jonbro/Audcalc/Firmware/Instrument.cc

#include "Instrument.h"
#include "AudioSampleSecondbloop.h"
#include "GlobalDefines.h"
#include "GrooveBox.h"
#include "audio/random.h"

static const uint16_t kPitchTableStart = 128 * 128;
static const uint16_t kOctave = 12 * 128;

void Instrument::Init(Midi *_midi, int16_t *temp_buffer)
{
    osc.Init(temp_buffer);
    currentSegment = ENV_SEGMENT_COMPLETE;
    osc.set_pitch(60<<7);
    osc.set_shape(MACRO_OSC_SHAPE_WAVE_MAP);
    osc.set_parameters(0,0);
    envPhase = 0;
    svf.Init();
    // svf.set_mode(SVF_MODE_HP);
    // svf.set_punch(0);
    midi = _midi;
    phase_ = 0;    
    sampleOffset = 0;
    env.Init();
    env.Trigger(ADSR_ENV_SEGMENT_DEAD);
    env2.Init();
    env2.Trigger(ADSR_ENV_SEGMENT_DEAD);
    portamentoEnv.Init();
    portamentoEnv.Trigger(ADSR_ENV_SEGMENT_DEAD);
}

const char *macroparams[16] = { 
    "Timb", "Filt", "VlPn", "Ptch",
    "Env", "EnvF", "EnvP", "EnvT",
    "?", "?", "?", "?",
    "?", "?", "FLTO", "TYPE"
};

const char *sampleparams[16] = { 
    "I/O", "FILT", "VlPn", "Ptch",
    "Env", "EnvF", "EnvP", "EnvT",
    "lop", "?", "?", "?",
    "?", "?", "FLTO", "TYPE"
};

// Values are defined in number of samples
void Instrument::SetAHD(uint32_t attackTime, uint32_t holdTime, uint32_t decayTime)
{
    this->attackTime = attackTime;
    this->holdTime = holdTime;
    this->decayTime = decayTime;
    env.Update(0x2b, 0x7f);
}

uint32_t Instrument::ComputePhaseIncrement(int16_t midi_pitch) {
  if (midi_pitch >= kPitchTableStart) {
    midi_pitch = kPitchTableStart - 1;
  }
  
  int32_t ref_pitch = midi_pitch;
  ref_pitch -= kPitchTableStart;
  
  size_t num_shifts = 0;
  while (ref_pitch < 0) {
    ref_pitch += kOctave;
    ++num_shifts;
  }
  
  uint32_t a = lut_sample_increments[ref_pitch >> 4];
  uint32_t b = lut_sample_increments[(ref_pitch >> 4) + 1];
  uint32_t phase_increment = a + \
      (static_cast<int32_t>(b - a) * (ref_pitch & 0xf) >> 4);
  phase_increment >>= num_shifts;
  return phase_increment;
}
q15_t Instrument::GetRawLfoValue()
{
    switch(lfo_shape)
    {
        case Lfo_Shape_RampUp:
            return (int16_t)(lfo_phase >> 16);
        case Lfo_Shape_RampDown:
            return -(int16_t)(lfo_phase >> 16);
        case Lfo_Shape_Triangle:
        {
            uint32_t p = lfo_phase;
            if (p >= 0x80000000u) p = 0xFFFFFFFFu - p;
            return (int16_t)((p >> 15) - 32767);
        }
        case Lfo_Shape_Square:
            return lfo_phase >= 0x80000000u ? (int16_t)0x7fff : (int16_t)-0x7fff;
        case Lfo_Shape_Random:
            return lfo_random_value;
        case Lfo_Shape_SampleGlide:
        {
            int32_t t = lfo_phase >> 16;
            return (int16_t)(((int32_t)lfo_random_prev * (65535 - t) + (int32_t)lfo_random_value * t) >> 16);
        }
        default: // Lfo_Shape_Sine
            return Interpolate824(wav_sine, lfo_phase);
    }
}
q15_t Instrument::GetLfoState()
{
    return mult_q15(GetRawLfoValue(), lfo_depth);
}
void __not_in_flash_func(Instrument::Render)(const uint8_t* sync, int16_t* buffer, size_t size)
{    
    q15_t param1_withMods = param1Base;
    q15_t param2_withMods = param2Base;
    q15_t cutoffWithMods = mainCutoff;
    q15_t pitchWithMods = pitch = Mix(pitchStart, pitchTarget, 65535-portamentoAmt);
    panWithMods = panning;
    volumeWithMods = volume;
    q15_t lfo = GetLfoState();
    switch(lfo1Target)
    {
        case Lfo_Target_Volume:
        {
            // lfo_depth maxes at ~0x3fff, so <<1 gives full q15 range.
            q15_t raw = GetRawLfoValue();
            q15_t norm = (raw >> 1) + 0x4000;  // [-1,1] -> [0,1] in q15
            q15_t D = lfo_depth << 1;           // full-range depth
            // scale: 1.0 at peak, (1-D) at trough
            q15_t scale = (0x7fff - D) + mult_q15(D, norm);
            volumeWithMods = mult_q15(volume, scale);
            break;
        }
        case Lfo_Target_Timbre:
            param1_withMods = add_q15(param1_withMods, lfo);
            break;
        case Lfo_Target_Color:
            param2_withMods = add_q15(param2_withMods, lfo);
            break;
        case Lfo_Target_Cutoff:
            cutoffWithMods = add_q15(cutoffWithMods, lfo);
            break;
        case Lfo_Target_Pitch:
            pitchWithMods = pitchWithMods+(lfo>>4);
            break;
        case Lfo_Target_Pan:
            panWithMods = add_q15(panWithMods, lfo);
            break;
        default:
            break;
    }

    // could alternately use tick rate stuff. might be way better
    // fast 4bf0000
    // slow fffff
    // holy hell what the fuck is this code, seriously :0
    // should like, maybe, move this into some class or something :P 
    uint32_t lfoPhaseIncrement = lut_tempo_phase_increment[songData->GetBpm()];
    // 24ppq
    lfoPhaseIncrement = lfoPhaseIncrement + (lfoPhaseIncrement>>1);
    lfoPhaseIncrement = lfoPhaseIncrement/((lfo_rate>>4)+2);
    //int32_t phaseOff = ((uint32_t)(0xffff-Interpolate824(lut_env_expo, (0x7fff-lfo_rate)<<16))<<13)-0x7fffff; 
    uint32_t old_phase = lfo_phase;
    lfo_phase += lfoPhaseIncrement;
    if (lfo_phase < old_phase) {  // wrapped — update S&H/SampleGlide random values
        lfo_random_prev = lfo_random_value;
        lfo_random_value = stmlib::Random::GetSample();
    }

    for (size_t i = 0; i < 2; i++)
    {
        EnvTargets t = i==0?env1Target:env2Target;
        int16_t depth = i==0?env1Depth:env2Depth;
        depth = (depth-0x4000)*2; // center at zero
        ADSREnvelope* e = i==0?&env:&env2;
        switch (t)
        {
            case Target_Volume:
                break;
            case Target_Timbre:
                param1_withMods = add_q15(param1_withMods, mult_q15(depth, e->valueLin()>>1));
                break;
            case Target_Color:
                param2_withMods = add_q15(param2_withMods, mult_q15(depth, e->valueLin()>>1));
                break;
            case Target_Cutoff:
                cutoffWithMods = add_q15(cutoffWithMods, mult_q15(depth, e->valueLin()>>1));
                break;
            case Target_Pitch:
                pitchWithMods = pitchWithMods+(mult_q15(depth, e->value()>>1)>>4);
                break;
            case Target_Pan:
                panWithMods = add_q15(panWithMods, mult_q15(depth, e->valueLin()>>1));
                break;
            default:
                break;
        }
    }
    
    if(param1_withMods < 0)
    {
        param1_withMods = 0;
    }
    if(param2_withMods < 0)
    {
        param2_withMods = 0;
    }
    if(cutoffWithMods < 0)
    {
        cutoffWithMods = 0;
    }
    pWithMods = cutoffWithMods; 
    svf.set_frequency(cutoffWithMods);

    if(instrumentType == INSTRUMENT_SAMPLE)
    {
        uint32_t filesize = ffs_file_size(GetFilesystem(), file);
        if(!file || filesize == 0 || sampleSegment == SMP_COMPLETE)
        {
            memset(buffer, 0, SAMPLES_PER_BLOCK*2);
            return;
        }
        // double check the file length
        if(!file->initialized || sampleOffset*2 > file->filesize)
            sampleSegment = SMP_COMPLETE;
        if(sampleSegment == SMP_COMPLETE)
        {
            for(int i=0;i<SAMPLES_PER_BLOCK;i++)
            {
                buffer[i] = 0;
            }
            return;
        }

        // this is too slow to do in the loop - which unfortunately makes
        // handling higher octaves quite difficult
        // one thing I could do is add a special read mode to change the stepping in the ffs_read to match the phase increment - i.e. read 1, skip 1 or something like this?
        // int16_t wave[128*5] = {0}; // lets just get 5 octaves worth? thats only 2k, we should be able to spare it, lol
        // ffs_seek(GetFilesystem(), file, sampleOffset*2);
        // // clamp the read amount to the maximum filesize
        // // todo: add a ffs_read that takes a per read stride, so I can fill this more easily, and don't need to load more than necessary
        // uint16_t readAmount = (sampleOffset*2+2*128*5)>filesize?filesize-sampleOffset*2:2*128*5;
        // ffs_read(GetFilesystem(), file, wave, readAmount);
        uint32_t startingSampleOffset = sampleOffset;
        for(int i=0;i<SAMPLES_PER_BLOCK;i++)
        {
            if(sampleOffset > sampleEnd - 1)
            {
                if(loopMode == INSTRUMENT_LOOPMODE_NONE)
                {
                    sampleSegment = SMP_COMPLETE;
                    buffer[i] = 0;
                    continue;
                }
                else
                {
                    while(sampleOffset*2 > filesize - 1)
                    {
                        sampleOffset -= filesize/2;
                    }
                }
            }
            int16_t wave;
            ffs_seek(GetFilesystem(), file, sampleOffset*2);
            ffs_read(GetFilesystem(), file, &wave, 2);

            phase_ += phase_increment;
            sampleOffset+=(phase_>>25);
            phase_-=(phase_&(0xfe<<24));

            buffer[i] = wave;//[sampleOffset-startingSampleOffset];
            
            if(microFade < 0xfa)
            {
                buffer[i] = (((int32_t)buffer[i]*microFade)>>8);
                microFade += 0xa;
            }
            // else
            // {
            //     lastSample = buffer[i];
            // }
        }
    }
    else if(instrumentType == INSTRUMENT_MACRO)
    {
        osc.set_pitch(pitchWithMods);
        osc.set_parameter_1(param1_withMods);
        osc.set_parameter_2(param2_withMods);
        osc.Render(sync, buffer, SAMPLES_PER_BLOCK);
    }
    RenderGlobal(sync, buffer, size);
}
void Instrument::RenderGlobal(const uint8_t* sync, int16_t* buffer, size_t size)
{
    int32_t volDelta = (int32_t)volumeWithMods - (int32_t)prevVolumeWithMods;
    for(int i=0;i<SAMPLES_PER_BLOCK;i++)
    {
        lastenv2val = env2.Render();
        lastenvval = env.Render();
        portamentoAmt = portamentoEnv.Render();
        q15_t envval = lastenvval >> 1;
        if(enable_env)
        {
            buffer[i] = mult_q15(buffer[i], envval);
        }
        // buffer[i] = Interpolate88(ws_violent_overdrive, buffer[i] + 32768);

        buffer[i] = svf.Process(buffer[i]);
        
        // not sure why distortion isn't working, revisit at some point
        // int32_t shiftedSample = mult_q15(buffer[i], f32_to_q15(0.5));// + distortionAmount; // I think this is the overdrive amount? 
        // buffer[i] = Interpolate88(ws_moderate_overdrive, shiftedSample);
        // buffer[i] = mult_q15(buffer[i], f32_to_q15(1));
        buffer[i] = mult_q15(buffer[i], retriggerVolume);
        q15_t vol_i = prevVolumeWithMods + volDelta * i / SAMPLES_PER_BLOCK;
        buffer[i] = mult_q15(buffer[i], vol_i);
    }
    prevVolumeWithMods = volumeWithMods;
}
bool Instrument::IsPlaying()
{
    if(env.segment() == ADSR_ENV_SEGMENT_DEAD)
        return false;
    if(instrumentType == INSTRUMENT_SAMPLE && sampleSegment == SMP_COMPLETE)
        return false;
    return true;
}

void Instrument::SetOscillator(uint8_t oscillator)
{
    osc.set_shape((MacroOscillatorShape)oscillator);
}

void Instrument::UpdateVoiceData(VoiceData &voiceData)
{
    uint8_t pv[VoiceData::PARAM_CACHE_SIZE];
    voiceData.FillResolvedParamCache(playingStep, playingPattern, lastPressedKey, pv, !liveTriggered);

    lfo1Target = (LfoTargets)(((uint16_t)pv[Lfo1Target] * Lfo_Target_Count) >> 8);

    delaySend = pv[DelaySend];
    reverbSend = pv[ReverbSend];
    volume = ((q15_t)pv[Volume]) << 7;
    panning = ((q15_t)pv[Pan]) << 7;
    portamentoParamAmt = pv[Portamento];
    fineTuneParamAmt = pv[FineTune];
    q15_t env1A = (q15_t)pv[AttackTime] << 7;
    q15_t env1D = (q15_t)pv[DecayTime] << 7;
    q15_t env2A = (q15_t)pv[AttackTime2] << 7;
    q15_t env2D = (q15_t)pv[DecayTime2] << 7;
    q15_t lfoState = GetLfoState();
    switch(lfo1Target)
    {
        case Lfo_Target_Env1Attack:
            env1A = add_q15(env1A, lfoState);
            break;
        case Lfo_Target_Env2Attack:
            env2A = add_q15(env2A, lfoState);
            break;
        case Lfo_Target_Env1Decay:
            env1D = add_q15(env1D, lfoState);
            break;
        case Lfo_Target_Env2Decay:
            env2D = add_q15(env1A, lfoState);
            break;
        case Lfo_Target_Env12Attack:
            env1A = add_q15(env1A, lfoState);
            env2A = add_q15(env2A, lfoState);
            break;
        case Lfo_Target_Env12Decay:
            env1D = add_q15(env1D, lfoState);
            env2D = add_q15(env1D, lfoState);
            break;
        default:
            break;
    }
    if(env1D < 0) env1D = 0;
    if(env1A < 0) env1A = 0;
    if(env2D < 0) env2D = 0;
    if(env2A < 0) env2A = 0;
    if(instrumentType == INSTRUMENT_SAMPLE || instrumentType == INSTRUMENT_MACRO)
    {
        env.Update(env1A>>8, env1D>>8);
        env2.Update(env2A>>8, env2D>>8);
        lfo_depth = (pv[LFODepth] >> 1) << 7;
        lfo_rate = (pv[LFORate] >> 1) << 7;
        lfo_shape = (pv[Lfo1Shape] * Lfo_Shape_Count) >> 8;
        mainCutoff = (pv[Cutoff] >> 1) << 7;
        svf.set_frequency(add_q15(mainCutoff, lastenv2val>>1));
        svf.set_resonance((pv[Resonance] >> 1) << 7);
        env1Target = (EnvTargets)(((uint16_t)pv[Env1Target] * Target_Count) >> 8);
        env1Depth = (q15_t)pv[Env1Depth] << 7;
        env2Target = (EnvTargets)(((uint16_t)pv[Env2Target] * Target_Count) >> 8);
        env2Depth = (q15_t)pv[Env2Depth] << 7;
        distortionAmount = (q15_t)pv[DelaySend] << 7;
    }
    if(voiceData.GetInstrumentType() == INSTRUMENT_MACRO)
    {
        param1Base = (q15_t)pv[Timbre] << 7;
        param2Base = (q15_t)pv[Color] << 7;
    }
}

void __not_in_flash_func(Instrument::TempoPulse)()
{
    if(TickRetriggers())
        Retrigger();
}
void Instrument::ClearRetriggers()
{
    retriggersRemaining = 0;
}
void __not_in_flash_func(Instrument::Retrigger)()
{
    if(playingVoice->GetInstrumentType() == INSTRUMENT_SAMPLE)
    { 
        sampleSegment = SMP_PLAYING;
        sampleOffset = lastTriggerSampleOffset;
        env.Trigger(ADSR_ENV_SEGMENT_ATTACK);
        env2.Trigger(ADSR_ENV_SEGMENT_ATTACK);
        retriggerVolume = add_q15(retriggerVolume, retriggerFade);
    }
    if(playingVoice->GetInstrumentType() == INSTRUMENT_MACRO)
    {
        enable_env = true;
        osc.Strike();
        env.Trigger(ADSR_ENV_SEGMENT_ATTACK);
        env2.Trigger(ADSR_ENV_SEGMENT_ATTACK);
        retriggerVolume = add_q15(retriggerVolume, retriggerFade);
    }
}

// The glide length arrives in twenty-fourths of a sequencer step Convert it
// into the increment that walks portamentoEnv in samples.
uint32_t Instrument::ComputePortamentoIncrement(uint16_t twentyFourths, VoiceData &voiceData)
{
    uint32_t stepPulses = GrooveBox::getTickCountForRateIndex((voiceData.GetRateForPattern(playingPattern)*7)>>8);
    // the stored bpm sits one below the displayed tempo
    uint32_t bpm = (uint32_t)songData->GetBpm()+1;
    // The instrument clock is 96ppq, so one pulse is (rate*60)/(bpm*96) samples.
    uint64_t samples = ((uint64_t)stepPulses * twentyFourths * AUDIO_SAMPLE_RATE * 60) / ((uint64_t)24 * bpm * 96);
    if(samples < 1)
        samples = 1;
    uint64_t increment = ((uint64_t)1 << 39) / samples;
    if(increment > 0xffffffff)
        increment = 0xffffffff;
    // Render() shifts by 7 before stepping, so we clamp this to a minimum of 1 increment so the pitch bend doesnt stall
    if(increment < 128)
        increment = 128;
    return (uint32_t)increment;
}

void __not_in_flash_func(Instrument::NoteOn)(uint8_t key, int16_t midinote, uint8_t step, uint8_t pattern, bool livePlay, VoiceData &voiceData)
{
    if(livePlay)
    {
        lastPressedKey = key;
    }
    liveTriggered = livePlay;
    playingStep = step;
    playingPattern = pattern;
    playingVoice = &voiceData;
    int note = midinote;
    // resolves this step's locks in a single walk of the chain
    uint8_t pv[VoiceData::PARAM_CACHE_SIZE];
    voiceData.FillResolvedParamCache(playingStep, playingPattern, lastPressedKey, pv, !liveTriggered);
    ArmRetriggers(pv);
    if(voiceData.GetInstrumentType() == INSTRUMENT_SAMPLE)
    {
        microFade = 0;
        UpdateVoiceData(voiceData);
        playingSlice = key;
        file = voiceData.GetFile();
        instrumentType = voiceData.GetInstrumentType();
        uint32_t filesize = ffs_file_size(GetFilesystem(), file);
        if(voiceData.GetSampler() != SAMPLE_PLAYER_PITCH)
        {
            note = 69; // need to figure out a way to fine tune for non-pitched samples
        }
        else
        {
            // clamp it - what kind of wild person needs so many octaves anyways.
            note = note>69+12*4?69+12*4:note;
            key = {0};
        }
        if(voiceData.GetSampler() == SAMPLE_PLAYER_SEQL)
        {
            sampleOffset = (voiceData.GetSampleStart(0)) * (filesize>>9);
            sampleEnd = sampleOffset + (voiceData.GetSampleLength(0)) * (filesize>>9);
            if(sampleEnd*2 > filesize - 1)
            {
                sampleEnd = filesize/2 -1;
            }
            // compute the phase increment so it loops in 16 beats
            // first we need to know the number of samples in the loop?
            uint32_t tempoPhaseIncrement = lut_tempo_phase_increment[songData->GetBpm()];
            // 24ppq
            tempoPhaseIncrement = tempoPhaseIncrement + (tempoPhaseIncrement>>1);
            uint32_t tempoPhase = 0;
            uint32_t sampleCount = 0;
            uint8_t beatCount = 0;
            while(beatCount < 6*16)
            {
                tempoPhase += tempoPhaseIncrement;
                sampleCount+=SAMPLES_PER_BLOCK;
                if((tempoPhase >> 31) > 0)
                {
                    tempoPhase &= 0x7fffffff;
                    beatCount++;
                }
            }
            sampleCount-=256;
            phase_increment = (uint32_t)(((uint64_t)(sampleEnd-sampleOffset)<<31)/((uint64_t)sampleCount)); // q32?
            phase_increment = phase_increment>>6; // q25 our overflow value
            // calculate the actual sample offset based on the pressed key
            lastTriggerSampleOffset = sampleOffset = (sampleEnd-sampleOffset)/16*key+sampleOffset;//((uint64_t)sampleCount)*((uint32_t)(key))/(uint32_t)16+sampleOffset;
        }
        else
        {
            sampleOffset = (voiceData.GetSampleStart(key)) * (filesize>>9);
            sampleEnd = sampleOffset + (voiceData.GetSampleLength(key)) * (filesize>>9);
            if(sampleEnd*2 > filesize - 1)
            {
                sampleEnd = filesize/2 -1;
            }
            phase_increment = ComputePhaseIncrement(note<<7);
        }
        // printf("sample points in %i out %i filesize %i\n", sampleOffset, sampleEnd, filesize);
        // just hardcode note to 69 for now
        phase_ = 0;
        sampleSegment = SMP_PLAYING;
        env.Trigger(ADSR_ENV_SEGMENT_ATTACK);
        env2.Trigger(ADSR_ENV_SEGMENT_ATTACK);
    }
    if(voiceData.GetInstrumentType() == INSTRUMENT_MACRO)
    {
        // copy parameters from voice
        UpdateVoiceData(voiceData);
        // only set shape on initial trigger
        osc.set_shape(voiceData.GetShape());
        enable_env = true;
        pitchTarget = (note<<7)+((fineTuneParamAmt-0x80)<<1);
        pitchStart = pitch;
        uint16_t glideTwentyFourths = portamentoTwentyFourths[PORTAMENTO_INDEX(portamentoParamAmt)];
        if(glideTwentyFourths == 0)
        {
            // off: park the envelope so the note starts on pitch
            portamentoEnv.Trigger(ADSR_ENV_SEGMENT_DEAD);
            pitch = pitchStart = pitchTarget;
        }
        else
        {
            // only the decay matters here, the attack segment is never triggered
            portamentoEnv.SetDecayIncrement(ComputePortamentoIncrement(glideTwentyFourths, voiceData));
            portamentoEnv.Trigger(ADSR_ENV_SEGMENT_DECAY);
        }
        osc.set_pitch(pitch);
        instrumentType = voiceData.GetInstrumentType();
        osc.Strike();
        env.Trigger(ADSR_ENV_SEGMENT_ATTACK);
        env2.Trigger(ADSR_ENV_SEGMENT_ATTACK);
    }
    lastNoteOnPitch = note;
}
