jonbro/Audcalc/Firmware/audio/resources.cc

// Copyright 2012 Emilie Gillet.
//
// Author: Emilie Gillet (emilie.o.gillet@gmail.com)
//
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
// See http://creativecommons.org/licenses/MIT/ for more information.
//
// -----------------------------------------------------------------------------
//
// Resources definitions.
//
// Automatically generated with:
// make resources


#include "audio/resources.h"

namespace braids {

static const char str_dummy[] = "dummy";


const char* string_table[] = {
  str_dummy,
};

const uint16_t lut_resonator_coefficient[] = {
   65535,  65535,  65535,  65535,
   65535,  65535,  65535,  65535,
   65535,  65535,  65534,  65534,
   65534,  65534,  65534,  65534,
   65533,  65533,  65533,  65532,
   65532,  65532,  65531,  65531,
   65530,  65529,  65529,  65528,
   65527,  65526,  65525,  65523,
   65522,  65520,  65518,  65516,
   65514,  65511,  65508,  65505,
   65501,  65497,  65492,  65487,
   65481,  65474,  65467,  65458,
   65449,  65438,  65427,  65413,
   65398,  65381,  65363,  65341,
   65318,  65291,  65261,  65228,
   65190,  65148,  65100,  65047,
   64987,  64920,  64845,  64761,
   64666,  64560,  64440,  64307,
   64157,  63989,  63800,  63589,
   63352,  63086,  62788,  62454,
   62080,  61661,  61192,  60667,
   60079,  59421,  58686,  57864,
   56945,  55920,  54775,  53499,
   52078,  50496,  48737,  46784,
   44617,  42219,  39568,  36644,
   33426,  29894,  26028,  21812,
   17232,  12280,   6953,   1259,
       0,      0,      0,      0,
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
   24712,  18568,     24,     40,
   60416,  10308,   4368,   3616,
   64520,  64516,  65024,  64768,
   64640,  64576,  64544,  64528,
   49152,  57344,  28672,  14336,
    6144,   7168,  35840,  50176,
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
};


const uint16_t* char_table[] = {
  chr_characters,
};


}  // namespace braids
