jonbro/Audcalc/Firmware/m6x118pt7b.cc

#include "m6x118pt7b.h"

const uint8_t m6x118pt7bBitmaps[] = {
  0x00, 0xFF, 0xFF, 0x3C, 0xDE, 0xD2, 0x6C, 0xD9, 0xB7, 0xFF, 0xED, 0xBF,
  0xFF, 0x6C, 0xD9, 0xB0, 0x30, 0xC7, 0xFF, 0xC3, 0xE7, 0xC3, 0xFF, 0xE3,
  0x0C, 0xC3, 0x31, 0xCE, 0x73, 0x8C, 0xC3, 0x3C, 0x3F, 0x19, 0x8C, 0xC7,
  0xE7, 0xEF, 0x7F, 0x9E, 0xCE, 0x7F, 0xDE, 0xE0, 0xF4, 0x7F, 0xCC, 0xCC,
  0xCC, 0xCC, 0xCF, 0x70, 0xEF, 0x33, 0x33, 0x33, 0x33, 0x3F, 0xE0, 0xDF,
  0xDD, 0xFD, 0x80, 0x30, 0xCF, 0xFF, 0x30, 0xC0, 0xF4, 0xFF, 0xF0, 0xF0,
  0x0C, 0x31, 0xC6, 0x38, 0xC7, 0x18, 0xE3, 0x0C, 0x00, 0x7B, 0xFC, 0xF3,
  0xCF, 0x3C, 0xF3, 0xCF, 0xF7, 0x80, 0x33, 0xCF, 0x0C, 0x30, 0xC3, 0x0C,
  0x33, 0xFF, 0xC0, 0x7B, 0xFC, 0xC3, 0x0C, 0x73, 0x9C, 0xE3, 0xFF, 0xC0,
  0x7B, 0xFC, 0xC3, 0x38, 0xF0, 0xC3, 0xCF, 0xF7, 0x80, 0xCF, 0x3C, 0xF3,
  0xCF, 0xF7, 0xC3, 0x0C, 0x30, 0xC0, 0xFF, 0xFC, 0x30, 0xFB, 0xF0, 0xC3,
  0x0F, 0xFF, 0x80, 0x7B, 0xFC, 0xF0, 0xFB, 0xFC, 0xF3, 0xCF, 0xF7, 0x80,
  0xFF, 0xF0, 0xC3, 0x1C, 0x63, 0x8C, 0x30, 0xC3, 0x00, 0x7B, 0xFC, 0xF3,
  0x7B, 0xFC, 0xF3, 0xCF, 0xF7, 0x80, 0x7B, 0xFC, 0xF3, 0xCF, 0xF7, 0xC3,
  0xCF, 0xF7, 0x80, 0xF0, 0x0F, 0xF0, 0x0F, 0x40, 0x19, 0xDD, 0xCE, 0x38,
  0xE3, 0xFF, 0xF0, 0x00, 0xFF, 0xF0, 0xC7, 0x1C, 0x73, 0xBB, 0x98, 0x7B,
  0xFC, 0xC3, 0x1C, 0xE3, 0x0C, 0x00, 0xC3, 0x00, 0x3E, 0x3F, 0xB8, 0xF9,
  0xFD, 0xFE, 0xDF, 0x7F, 0x9E, 0xE0, 0x3F, 0xCF, 0xE0, 0x7B, 0xFC, 0xF3,
  0xCF, 0xFF, 0xF3, 0xCF, 0x3C, 0xC0, 0xFB, 0xFC, 0xF3, 0xFF, 0xEC, 0xF3,
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
                                        // digit cc number still fits the label column

const GFXfont m6x118pt7b = {
  (uint8_t  *)m6x118pt7bBitmaps,
  (GFXglyph *)m6x118pt7bGlyphs,
  0x20, 0x7F, 15 };

// Approx. 1365 bytes
