jonbro/Audcalc/Firmware/filesystem.h

#ifndef filesystem_H_
#define filesystem_H_

#include "hardware/flash.h"
#include "hardware/dma.h"
#include "hardware/irq.h"
#include "pico/multicore.h"
#include <stdio.h>
#include <string.h>

#ifdef __cplusplus
#include <cassert>
extern "C" {
#else
#include <assert.h>
#endif

/*

very limited file system, but I have different requirements:
- no erasing in the hotloop
- append only files
- guarenteed write size of 256 bytes
- REQUIRES WRITE SIZE OF 256!!!

*/

#define BLOCK_SIZE 0x1000
#define EMPTY_BLOCK 0xffffffff

typedef struct
{
    int     (*erase)  (uint32_t offset, size_t size);
    int      (*read)   (uint32_t offset, size_t size, void *dst);
    int      (*write)  (uint32_t offset, size_t size, void *buffer);
    uint32_t offset;
    uint32_t size;
    uint32_t empty_search_offset; // used to describe where searching for empty blocks starts, provide a random number to get some amount of flash leveling
} ffs_cfg;

typedef struct
{
    bool        initialized;
    uint16_t    object_id;
    
    uint32_t    filesize;
    uint32_t    logical_read_offset; // where we are in the file (disconnected from physical address)
    uint8_t     inblock_read_offset;
    uint32_t    read_block; // block holding logical_read_offset. moved by ffs_seek, read side only
    uint32_t    last_block; // tail of the chain, where ffs_append writes. EMPTY_BLOCK when !initialized
} ffs_file;

typedef struct
{
   int     (*erase)  (uint32_t offset, size_t size);
   int      (*read)   (uint32_t offset, size_t size, void *dst);
   int      (*write)  (uint32_t offset, size_t size, void *buffer);
   uint32_t offset;
   uint32_t size;
   void     *work_buf;
   uint32_t empty_search_offset; // used to describe where searching for empty blocks starts, provide a random number to get some amount of flash leveling
} ffs_filesystem;

typedef struct 
{
    uint16_t    object_id;
    uint16_t    written_page_mask;
    uint32_t    next_block;
     // also 0xff defines initial page
    uint32_t    prior_block;
} ffs_blockheader;


/* each block contains

block header
------------
object id - if 0xff then free.
jump page - offset of the next page that contains data for this object (0xff if the object ends within this page)
active page bitmask
initial page - 0x01

*/

#ifdef FFS_STATIC
#define FFS_DEF static
#else
#define FFS_DEF extern
#endif

FFS_DEF int ffs_mount(ffs_filesystem *fs, const ffs_cfg *cfg, void *work_buf);
FFS_DEF int ffs_open(ffs_filesystem *fs, ffs_file *file, uint16_t file_id);
FFS_DEF int ffs_append(ffs_filesystem *fs, ffs_file *file, void *buffer, size_t size);
FFS_DEF int ffs_seek(ffs_filesystem *fs, ffs_file *file, size_t position);
FFS_DEF int ffs_read(ffs_filesystem *fs, ffs_file *file, void *buffer, size_t size);
FFS_DEF int ffs_erase(ffs_filesystem *fs, ffs_file *file);
FFS_DEF int ffs_file_size(ffs_filesystem *fs, ffs_file *file);

#ifdef FFS_IMPLEMENTATION
// these should return some kind of error code on failure
// no formatting, we assume things have been cleaned up for us in advance of writing
FFS_DEF int ffs_mount(ffs_filesystem *fs, const ffs_cfg *cfg, void *work_buf)
{
    // empty search offset needs to be aligned to the block size
    uint32_t empty_search_offset_aligned = cfg->empty_search_offset+(BLOCK_SIZE-cfg->empty_search_offset%BLOCK_SIZE);
    empty_search_offset_aligned = empty_search_offset_aligned%cfg->size;
    // copy cfg into our filesystem
    fs->erase = cfg->erase;
    fs->write = cfg->write;
    fs->read = cfg->read;
    fs->offset = cfg->offset;
    fs->size = cfg->size;
    fs->empty_search_offset = empty_search_offset_aligned;
    fs->work_buf = work_buf;
}

static int16_t ffs_find_empty_page(ffs_blockheader *blockheader)
{
    int foundPage = -1;
    // find the first empty page
    for (size_t i = 0; i < 15; i++)
    {
        if((~blockheader->written_page_mask & (1<<i)) == 0)
        {
            foundPage = i;
            break;
        }
    }
    return foundPage;
}

inline FFS_DEF uint32_t ffs_file_read_block_logical_start(ffs_filesystem *fs, ffs_file *file)
{
    return file->logical_read_offset-(file->logical_read_offset%(256*15));
}

inline FFS_DEF bool ffs_block_valid(ffs_filesystem *fs, uint32_t block)
{
    // confirm the block is within the filesystem and aligned to a block boundary
    return block < fs->size && (block % BLOCK_SIZE) == 0;
}

FFS_DEF int ffs_open(ffs_filesystem *fs, ffs_file *file, uint16_t file_id)
{
    // cannot use the top bit of the file id, used for marking dead pages
    assert((file_id & 0x8000) == 0);
    // search the blocks for the start block that contains this id
    bool found = false;
    bool corrupt = false;
    uint32_t block_offset = 0;
    ffs_blockheader blockHeader;
    while(block_offset < fs->size)
    {
        fs->read(block_offset, sizeof(ffs_blockheader), &blockHeader);
        // need to check if it is the first block in the file, since we need to walk the tree to get the filesize
        // this requires a full filesystem scan when checking
        if(blockHeader.object_id == file_id && blockHeader.prior_block == EMPTY_BLOCK)
        {
            found = true;
            file->read_block         = block_offset;
            file->inblock_read_offset   = 0;
            file->logical_read_offset   = 0; 
            // need to walk the filetree to generate the filesize
            file->filesize              = 0;
            file->initialized           = true;
            int writtenPages = ffs_find_empty_page(&blockHeader);
            if(writtenPages >= 0)
            {
                file->filesize+=writtenPages*256;
            }
            else
            {
                file->filesize+=15*256;
            }
            // do extra walking to:
            // find the end of the file
            // find the file size
            // determine if there are any loop in the file
            uint32_t tail = block_offset;
            uint32_t block_jumps = fs->size/BLOCK_SIZE;
            while(blockHeader.next_block != EMPTY_BLOCK)
            {
                // if we have an invalid block or we have walked more blocks than the filesystem has, then the file is corrupt.
                if(!ffs_block_valid(fs, blockHeader.next_block) || block_jumps-- == 0)
                {
                    corrupt = true;
                    break;
                }
                tail = blockHeader.next_block;
                fs->read(tail, sizeof(ffs_blockheader), &blockHeader);
                int writtenPages = ffs_find_empty_page(&blockHeader);
                if(writtenPages >= 0)
                {
                    file->filesize+=writtenPages*256;
                }
                else
                {
                    file->filesize+=15*256;
                }
            }
            file->last_block = tail;
            break;
        }
        block_offset += BLOCK_SIZE;
    }
    if(!found || corrupt)
    {
        file->initialized = false;
        file->filesize = 0;
        // no tail to append to. ffs_append checks this before using it
        file->last_block = EMPTY_BLOCK;
    }
    file->object_id = file_id;
    // we set object id so that that if the file is corrupt we can clean it up with an erase.
    return corrupt?-1:0;
}

static int ffs_find_empty_block(ffs_filesystem *fs, uint32_t search_start, uint32_t fssize)
{
    uint32_t block_offset = 0;
    ffs_blockheader blockHeader;
    uint32_t readPos = fs->empty_search_offset; // this will be set to be lower than fssize at init time
    while(block_offset < fssize)
    {
        fs->read(readPos, sizeof(ffs_blockheader), &blockHeader);
        // find empty block?
        if(blockHeader.object_id == 0xffff)
        {
            return readPos;
        }
        block_offset += BLOCK_SIZE;
        readPos = readPos+BLOCK_SIZE;
        // ffsize is larger than the valid space, so we need to check if we are equal or greater
        if(readPos>=fssize)
        {
            readPos-=fssize;
        }
    }
    return -1;
}

FFS_DEF int ffs_append(ffs_filesystem *fs, ffs_file *file, void *buffer, size_t size)
{
    uint32_t block_offset = 0;
    ffs_blockheader blockHeader;
    if(!file->initialized)
    {
        // find a new empty block to write into
        int block_offset = ffs_find_empty_block(fs, 0, fs->size);
        if(block_offset < 0)
        {
            return -1;
        }
        blockHeader.object_id = file->object_id;
        blockHeader.next_block = EMPTY_BLOCK;
        blockHeader.prior_block = EMPTY_BLOCK;
        blockHeader.written_page_mask = ~1; // mark the first page as filled - this is done in inverted
        //blockHeader.block_logical_start = 0;
        // we are wasting a crapton of space here, but its ok?
        // easier just to waste and keep everything aligned rather than doing a bunch of copies at this point

        memset(fs->work_buf, 0xff, 256);
        memcpy(fs->work_buf, &blockHeader, sizeof(ffs_blockheader));
        fs->write(block_offset, 256, fs->work_buf);
        // step forward to the next 256 byte aligned chunks

        // need to handle going out of the block, but for now we can safely write into this chunk 
        // in fact - if we never write more than 256, we can safely just use this
        memset(fs->work_buf, 0xff, 256);
        memcpy(fs->work_buf, buffer, size);
        fs->write(block_offset+256, 256, fs->work_buf);
        file->read_block = block_offset;
        file->last_block = block_offset;
        file->inblock_read_offset = 0;
        file->logical_read_offset = 0;
        file->initialized = true;
        file->filesize+=256;
        return 0;
    }
    else
    {
        // start from the tail of the file
        block_offset = file->last_block;
        if(!ffs_block_valid(fs, block_offset))
        {
            // initialized with no usable tail - this is a corrupt file in this case
            return -1;
        }
        fs->read(block_offset, sizeof(ffs_blockheader), &blockHeader);
        if(blockHeader.object_id != file->object_id)
        {
            // the block header doesn't match the file we expected, corrupt
            return -1;
        }
        // another corruption check - if last_block didn't actually point to the end of the file
        // we move forward. Block jumps confirms no loops. This should normally be a no-op
        uint32_t block_jumps = fs->size/BLOCK_SIZE;
        while(blockHeader.next_block != EMPTY_BLOCK)
        {
            if(!ffs_block_valid(fs, blockHeader.next_block) || block_jumps-- == 0)
            {
                // corrupt chain, we have no tail to append to
                return -1;
            }
            block_offset = blockHeader.next_block;
            fs->read(block_offset, sizeof(ffs_blockheader), &blockHeader);
        }
        file->last_block = block_offset;

        // find the page in the tail block to write into
        int foundPage = ffs_find_empty_page(&blockHeader);
        if(foundPage < 0)
        {
            // the block is full, so create a new file
            int empty = ffs_find_empty_block(fs, 0, fs->size);
            if(empty < 0)
            {
                return -1;
            }
            // point the old tail at the new block
            blockHeader.next_block = empty;
            memset(fs->work_buf, 0xff, 256);
            memcpy(fs->work_buf, &blockHeader, sizeof(ffs_blockheader));
            fs->write(block_offset, 256, fs->work_buf);

            // build the blockheader
            blockHeader.object_id = file->object_id;
            blockHeader.next_block = EMPTY_BLOCK;
            blockHeader.prior_block = block_offset;
            block_offset = empty;
            file->last_block = block_offset;
            foundPage = 0;
        }
        //update the pagemask
        blockHeader.written_page_mask = ~(1<<foundPage);
        memset(fs->work_buf, 0xff, 256);
        memcpy(fs->work_buf, &blockHeader, sizeof(ffs_blockheader));
        fs->write(block_offset, 256, fs->work_buf);

        // write the data into the correct page!
        memset(fs->work_buf, 0xff, 256);
        memcpy(fs->work_buf, buffer, 256);
        fs->write(block_offset+(foundPage+1)*256, 256, fs->work_buf);
        file->filesize+=256;
        return 0;
    }
}

FFS_DEF int __not_in_flash_func(ffs_erase)(ffs_filesystem *fs, ffs_file *file)
{
    // find any blocks that have this file in them and remove
    uint32_t block_offset = 0;
    ffs_blockheader blockHeader;
    bool found = false;
    while(block_offset < fs->size)
    {
        fs->read(block_offset, sizeof(ffs_blockheader), &blockHeader);
        // found matching block
        if(blockHeader.object_id == file->object_id)
        {
            fs->erase(block_offset, BLOCK_SIZE);
            found = true;
        }
        block_offset+=BLOCK_SIZE;
    }
    // lets just make sure its all unitialized anyways
    file->initialized = false;
    file->inblock_read_offset   = 0;
    file->logical_read_offset   = 0;
    file->filesize              = 0;
    // the blocks are gone, so there is no tail any more. the next append takes
    // the !initialized branch and allocates a fresh one.
    file->last_block            = EMPTY_BLOCK;
    if(found)
    {
        return 0;
    }
    return -1;
}

static int ffs_load_blockheader(ffs_filesystem *fs, ffs_file *file, ffs_blockheader *blockheader)
{
    ffs_blockheader headerForSize;
    fs->read(file->read_block, sizeof(headerForSize), blockheader);
}

inline FFS_DEF int ffs_seek(ffs_filesystem *fs, ffs_file *file, size_t position)
{
    // early out if logical read position already set correctly
    if(file->logical_read_offset == position)
    {
        return 0;
    }
    // early out if read position is past end of file
    if(position >= file->filesize)
    {
        return -1;
    }
    // load blockheader
    ffs_blockheader blockHeader;

    fs->read(file->read_block, sizeof(blockHeader), &blockHeader);
    uint32_t read_block_logical_start = ffs_file_read_block_logical_start(fs, file);
    if(position >= read_block_logical_start)
    {
        // seeking forward
        if(position-read_block_logical_start < 256*15)
        {
            // if the read position is within the current block, we can just move things forward
            file->logical_read_offset = position;
            return 0;
        }
        else
        {
            // we are going forward to a later block
            // cap the number of block jumps so that we can detect loops in the blocks
            uint32_t block_jumps = fs->size/BLOCK_SIZE;
            while(blockHeader.next_block != EMPTY_BLOCK)
            {
                if(!ffs_block_valid(fs, blockHeader.next_block) || block_jumps-- == 0)
                {
                    return -1;
                }
                file->read_block = blockHeader.next_block;
                fs->read(file->read_block, sizeof(blockHeader), &blockHeader);
                read_block_logical_start += 256*15;
                if(position-read_block_logical_start < 256*15)
                {
                    // if the read position is within the current block, we can just move things forward
                    file->logical_read_offset = position;
                    return 0;
                }
            }
            // we shouldn't hit this, it should have caught this error because we are asking for something
            // past the end of the file
            // Asserts don't post on device when not in debug mode - just here for an eventual test rig
            assert(false);
            return -1;
        }
    }
    else
    {
        // seeking backwards
        uint32_t block_jumps = fs->size/BLOCK_SIZE;
        while(blockHeader.prior_block != EMPTY_BLOCK)
        {
            if(!ffs_block_valid(fs, blockHeader.prior_block) || block_jumps-- == 0)
            {
                return -1;
            }
            file->read_block = blockHeader.prior_block;
            fs->read(file->read_block, sizeof(blockHeader), &blockHeader);
            read_block_logical_start -= 256*15;
            if(position-read_block_logical_start < 256*15)
            {
                // if the read position is within the current block, we can just move things forward
                file->logical_read_offset = position;
                return 0;
            }
        }
        // we shouldn't hit this, it should have caught this error because we are asking for something
        // past the beginning of the file. Should be impossible to even do this, since we are using uints
        // anyways, asserts are for logical errors
        assert(false);
        return -1;
    }
    return -1;
}


inline FFS_DEF int ffs_file_size(ffs_filesystem *fs, ffs_file *file)
{
    return file->filesize;
}

FFS_DEF int ffs_read(ffs_filesystem *fs, ffs_file *file, void *buffer, size_t size)
{
    if(!file->initialized)
    {
        // file isn't initialized?
        return -1; // need better error codes
    }

    // need to actually keep track of read state!
    ffs_blockheader blockHeader;

    fs->read(file->read_block, sizeof(blockHeader), &blockHeader);
    assert(blockHeader.object_id == file->object_id);
    // TODO: replace this assert with something that actually works
    //assert(file->logical_read_offset >= blockHeader.block_logical_start);

    int read_position = file->logical_read_offset-ffs_file_read_block_logical_start(fs, file);    
    // clamp the read amount to the remaining in the block
    int next_read_amount = (read_position+size>256*15)?256*15-read_position:size;
    //printf("position: %i %i\n", read_position, next_read_amount);
    fs->read(read_position+file->read_block+256, next_read_amount, buffer);
    if(size-next_read_amount>0)
    {
        // this will advance the read to the next block
        ffs_seek(fs, file, next_read_amount+file->logical_read_offset);
        // kinda dangerous to recurse, but lets assume we aren't gonna overflow the stack, lol.
        return ffs_read(fs, file, ((uint8_t*)buffer)+next_read_amount, size-next_read_amount);
    }
    // advance the read position
    // ignore the boundary error at this point, even if it is out of bounds
    // the next file read will trigger the boundary error?
    ffs_seek(fs, file, file->logical_read_offset+size);
    return 0;
}
#endif //FFS_IMPLEMENTATION



int file_read(uint32_t offset, size_t size, void *buffer);
int file_write(uint32_t offset, size_t size, void *buffer);
int file_erase(uint32_t offset, size_t size);

void TestFileSystem();
void InitializeFilesystem(bool fullClear, uint32_t empty_search_offset);

typedef struct 
{
    bool complete;
    int offset;
    int error;
} ffs_filesystemClearState;

#define ffs_filesystemClearState_init               {0, 0, 0}

bool DeleteNonEmpty(ffs_filesystemClearState *state);

ffs_filesystem* GetFilesystem();

#ifdef __cplusplus
}
#endif

#endif // filesystem_H_
