jonbro/Audcalc/Firmware/m6x1110pt7b.h

const uint8_t m6x1110pt7bBitmaps[] = {
  0x00, 0xFF, 0xFF, 0xFF, 0xFC, 0x7F, 0xC0, 0xEF, 0xBE, 0xD9, 0x77, 0x3B,
  0x9D, 0xCE, 0xEF, 0xFF, 0xFF, 0xDC, 0xEE, 0xFF, 0xFF, 0xDD, 0xCE, 0xE7,
  0x73, 0xB8, 0x38, 0x38, 0x38, 0x7F, 0xFF, 0xE0, 0xFC, 0xFC, 0x7F, 0x07,
  0xFF, 0xFC, 0xFC, 0x38, 0x38, 0xE0, 0xE7, 0x0F, 0x0C, 0x3C, 0x78, 0xF0,
  0xE7, 0xE7, 0x07, 0x3F, 0x07, 0xF1, 0xFE, 0x39, 0xC7, 0x38, 0xFF, 0x1F,
  0xDF, 0xFB, 0xEF, 0xFC, 0xFB, 0x9E, 0x73, 0xFF, 0xFE, 0xFB, 0xC0, 0xFF,
  0xB0, 0x7B, 0xFF, 0xCE, 0x73, 0x9C, 0xE7, 0x39, 0xCE, 0x73, 0xEF, 0x78,
  0xF7, 0xFE, 0x73, 0x9C, 0xE7, 0x39, 0xCE, 0x73, 0x9F, 0xFE, 0xF0, 0xEF,
  0xBF, 0xDE, 0xFF, 0xBE, 0xC0, 0x38, 0x38, 0x3F, 0xFF, 0xFF, 0x38, 0x38,
  0x38, 0xFF, 0xB0, 0xFF, 0xFF, 0xFF, 0xFF, 0x80, 0x07, 0x07, 0x07, 0x0F,
  0x0C, 0x3C, 0x38, 0x38, 0x78, 0x70, 0xF0, 0xE0, 0xE0, 0xE0, 0x7C, 0x7F,
  0xFF, 0xE7, 0xE7, 0xE7, 0xE7, 0xE7, 0xE7, 0xE7, 0xE7, 0xE7, 0xFF, 0x7C,
  0x38, 0x38, 0xF8, 0xF8, 0x38, 0x38, 0x38, 0x38, 0x38, 0x38, 0x38, 0x3F,
  0xFF, 0xFF, 0x7C, 0x7F, 0xFF, 0xE7, 0x07, 0x07, 0x07, 0x0F, 0x3C, 0x78,
  0xF0, 0xFF, 0xFF, 0xFF, 0x7C, 0x7F, 0xFF, 0xE7, 0x07, 0x3C, 0x3F, 0x3F,
  0x07, 0x07, 0xE7, 0xE7, 0xFF, 0x7C, 0xE7, 0xE7, 0xE7, 0xE7, 0xE7, 0xE7,
  0xE7, 0xFF, 0x7F, 0x07, 0x07, 0x07, 0x07, 0x07, 0xFF, 0xFF, 0xFF, 0xE0,
  0xE0, 0xFC, 0xFF, 0xFF, 0x07, 0x07, 0x07, 0x07, 0xFF, 0xFC, 0x7C, 0x7F,
  0xFF, 0xE7, 0xE0, 0xFC, 0xFF, 0xFF, 0xE7, 0xE7, 0xE7, 0xE7, 0xFF, 0x7C,
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
  {   407,   8,  14,   9,    0,  -13 },   // 0x46 'F'
  {   421,   8,  14,   9,    0,  -13 },   // 0x47 'G'
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

const GFXfont m6x1110pt7b = {
  (uint8_t  *)m6x1110pt7bBitmaps,
  (GFXglyph *)m6x1110pt7bGlyphs,
  0x20, 0x7E, 19 };

// Approx. 1771 bytes
