jonbro/Audcalc/Firmware/m6x1111pt7b.h

const uint8_t m6x1111pt7bBitmaps[] = {
  0x00, 0xFF, 0xFF, 0xFF, 0xFF, 0x8F, 0xF8, 0xEF, 0xDF, 0xBB, 0x30, 0x77,
  0x1D, 0xC7, 0x71, 0xDC, 0xFF, 0xFF, 0xFF, 0xFD, 0xDC, 0xFF, 0xFF, 0xFF,
  0xFD, 0xDC, 0x77, 0x1D, 0xC7, 0x70, 0x1C, 0x1C, 0x1C, 0x7F, 0xFF, 0xE0,
  0xE0, 0xFE, 0x7F, 0x7F, 0x07, 0xFF, 0xFE, 0xFE, 0x1C, 0x1C, 0xE0, 0xE7,
  0x0F, 0x0F, 0x1E, 0x7C, 0x70, 0xF0, 0xE7, 0x07, 0x07, 0x1F, 0x07, 0xFC,
  0x7F, 0xC7, 0x1C, 0x71, 0xC7, 0xFC, 0x7F, 0xCF, 0xF3, 0xEF, 0xFE, 0xFE,
  0xE7, 0xEE, 0x7C, 0xFF, 0xFF, 0xFF, 0x7E, 0xF0, 0xFF, 0xB0, 0x7F, 0xFF,
  0xF8, 0xE3, 0x8E, 0x38, 0xE3, 0x8E, 0x38, 0xE3, 0x8E, 0x3F, 0x7D, 0xF0,
  0xF3, 0xFF, 0xC7, 0x1C, 0x71, 0xC7, 0x1C, 0x71, 0xC7, 0x1C, 0x71, 0xFF,
  0xF3, 0xC0, 0xEF, 0xFF, 0xFB, 0xEF, 0xFD, 0xFB, 0x80, 0x1C, 0x1C, 0x1C,
  0xFF, 0xFF, 0xFC, 0x1C, 0x1C, 0xFF, 0xB0, 0xFF, 0xFF, 0xFF, 0xFF, 0x80,
  0x07, 0x07, 0x07, 0x0F, 0x0E, 0x1E, 0x1E, 0x1C, 0x7C, 0x70, 0x70, 0xF0,
  0xE0, 0xE0, 0xE0, 0x7E, 0xFF, 0xFF, 0xE7, 0xE7, 0xE7, 0xE7, 0xE7, 0xE7,
  0xE7, 0xE7, 0xE7, 0xFF, 0xFF, 0x7E, 0x1C, 0xFC, 0xFC, 0xFC, 0x1C, 0x1C,
  0x1C, 0x1C, 0x1C, 0x1C, 0x1C, 0x1C, 0xFF, 0xFF, 0xFF, 0x7E, 0xFF, 0xFF,
  0xE7, 0x07, 0x07, 0x07, 0x0F, 0x1E, 0x1C, 0x7C, 0xF0, 0xFF, 0xFF, 0xFF,
  0x7E, 0xFF, 0xFF, 0xE7, 0x07, 0x1E, 0x1E, 0x1F, 0x07, 0x07, 0x07, 0xE7,
  0xFF, 0xFF, 0x7E, 0xE7, 0xE7, 0xE7, 0xE7, 0xE7, 0xE7, 0xE7, 0xFF, 0x7F,
  0x7F, 0x07, 0x07, 0x07, 0x07, 0x07, 0xFF, 0xFF, 0xFF, 0xE0, 0xE0, 0xFE,
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
  {   448,   8,  15,  10,    0,  -14 },   // 0x46 'F'
  {   463,   8,  15,  10,    0,  -14 },   // 0x47 'G'
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

const GFXfont m6x1111pt7b = {
  (uint8_t  *)m6x1111pt7bBitmaps,
  (GFXglyph *)m6x1111pt7bGlyphs,
  0x20, 0x7E, 21 };

// Approx. 1886 bytes
