jonbro/Audcalc/Firmware/m6x1116pt7b.h

#ifndef M6X11FONT_INCLUDE
#define M6X11FONT_INCLUDE

const uint8_t m6x1116pt7bBitmaps[] = {
  0x00, 0xFF, 0xFF, 0xFF, 0xFF, 0xFF, 0xFF, 0xFF, 0xF0, 0x0F, 0xFF, 0xF0,
  0xF3, 0xFC, 0xFF, 0x3F, 0xCF, 0x30, 0xCC, 0x30, 0x3C, 0xF0, 0xF3, 0xC3,
  0xCF, 0x0F, 0x3C, 0x3C, 0xF0, 0xF3, 0xFF, 0xFF, 0xFF, 0xFF, 0xFF, 0xFC,
  0xF3, 0xC3, 0xCF, 0x3F, 0xFF, 0xFF, 0xFF, 0xFF, 0xFF, 0xFF, 0xCF, 0x3C,
  0x3C, 0xF0, 0xF3, 0xC3, 0xCF, 0x0F, 0x3C, 0x3C, 0xF0, 0x0F, 0x00, 0xF0,
  0x0F, 0x00, 0xF0, 0x3F, 0xF3, 0xFF, 0xFF, 0xFF, 0x00, 0xF0, 0x0F, 0xFC,
  0xFF, 0xC3, 0xFF, 0x3F, 0xF0, 0x0F, 0x00, 0xFF, 0xFF, 0xFF, 0xFF, 0xFC,
  0xFF, 0xC0, 0xF0, 0x0F, 0x00, 0xF0, 0x0F, 0x00, 0xF0, 0x0F, 0x0F, 0xF0,
  0xF0, 0x3F, 0x03, 0xF0, 0xFC, 0x0F, 0xC3, 0xF0, 0x3F, 0x0F, 0xC0, 0xFC,
  0x0F, 0x0F, 0xF0, 0xF0, 0x0F, 0x00, 0xF0, 0x0F, 0xF0, 0x07, 0xF8, 0x0F,
  0xFF, 0x07, 0xFF, 0x83, 0xC3, 0xC1, 0xE1, 0xE0, 0xF0, 0xF0, 0x7F, 0xF8,
  0x3F, 0xFC, 0x7F, 0xF9, 0xFF, 0xFC, 0xFE, 0x7F, 0xFF, 0x3F, 0xFF, 0x87,
  0xFB, 0xC3, 0xFD, 0xE1, 0xF8, 0xF0, 0xFC, 0x7F, 0xFF, 0xFF, 0xFF, 0xE7,
  0xF9, 0xF3, 0xFC, 0xF8, 0xFF, 0xFF, 0x33, 0x3F, 0x3F, 0xFF, 0xFF, 0xF0,
  0xF0, 0xF0, 0xF0, 0xF0, 0xF0, 0xF0, 0xF0, 0xF0, 0xF0, 0xF0, 0xF0, 0xF0,
  0xF0, 0xF0, 0xF0, 0xF0, 0xFF, 0xFF, 0x3F, 0x3F, 0xFC, 0xFC, 0xFF, 0xFF,
  0x0F, 0x0F, 0x0F, 0x0F, 0x0F, 0x0F, 0x0F, 0x0F, 0x0F, 0x0F, 0x0F, 0x0F,
  0x0F, 0x0F, 0x0F, 0x0F, 0x0F, 0xFF, 0xFF, 0xFC, 0xFC, 0xF3, 0xFC, 0xFF,
  0xFF, 0xFF, 0x3F, 0x0F, 0xFF, 0xFF, 0xCF, 0xF3, 0xC0, 0x0F, 0x00, 0xF0,
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
  {   918,  12,  21,  14,    0,  -20 },   // 0x46 'F'
  {   950,  12,  21,  14,    0,  -20 },   // 0x47 'G'
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

const GFXfont m6x11font = {
  (uint8_t  *)m6x1116pt7bBitmaps,
  (GFXglyph *)m6x1116pt7bGlyphs,
  0x20, 0x7E, 30 };

// Approx. 3188 bytes
#endif //M6X11FONT_INCLUDE
