jonbro/Audcalc/Firmware/SongData.cc

#include "SongData.h"
#include "m6x118pt7b.h"

SyncMode SongData::GetSyncOutMode(){
    uint8_t bareSyncMode = ((((uint16_t)internalData.syncOut)*6) >> 8);
    SyncMode mode = SyncModeNone;
    switch(bareSyncMode)
    {
        case 1:
            mode = SyncModeMidi;
            break;
        case 2:
            mode = (SyncMode)(SyncModeMidi | SyncModePO);
            break;
        case 3:
            mode = (SyncMode)(SyncModeMidi | SyncMode4PQ);
            break;
        // PO
        case 4:
            mode = SyncModePO;
            break;
        // 4ppq
        case 5:
            mode = SyncMode4PQ;
            break;
    }
    return mode;
}
SyncMode SongData::GetSyncInMode(){
    uint8_t bareSyncMode = ((((uint16_t)internalData.syncIn)*4) >> 8);
    SyncMode mode = SyncModeNone;
    switch(bareSyncMode)
    {
        case 1:
            mode = SyncModeMidi;
            break;
        // PO
        case 2:
            mode = SyncModePO;
            break;
        // 4ppq
        case 3:
            mode = SyncMode4PQ;
            break;
    }
    return mode;
}

uint8_t& SongData::GetParam(uint8_t param, uint8_t pattern)
{
    switch(param)
    {
        case 1*2:
            return internalData.changeLength[pattern];
        
        case 19*2:
            return internalData.bpm;
        case 19*2+1:         // 39 — B knob, play page 1
            return internalData.swing;

        case 19*2+(25*2):    // 88 — A knob, play page 2
            return internalData.syncIn;
        case 19*2+1+(25*2):  // 89 — B knob, play page 2
            return internalData.syncOut;

        case 69*2:           // 138 — A knob, play page 3
            return internalData.hpVol;

        case 22*2+(25*2): // this offset to the next page must also be doubled
            return internalData.delayFeedback;
        case 22*2+(25*2)+1: // this offset to the next page must also be doubled
            return internalData.delayTime;
        case 22*2+(25*2*2): // fx page 3 - the extra reverb controls
            return internalData.reverbFeedback;
        case 22*2+(25*2*2)+1:
            return internalData.reverbDamping;
        case 22*2+(25*2*3): // fx page 4 - reverb allpass modulation
            return internalData.reverbModulation;
        case 22*2+(25*2*3)+1:
            return internalData.reverbLongTail;
        case 24*2+(25*2): // this offset to the next page must also be doubled
            return internalData.scale;
        case 24*2+1:
            return internalData.root;
    }
    return nothing;
}
uint8_t SongData::GetRoot()
{
    return (internalData.root*12)>>8;
}
uint8_t SongData::GetScale()
{
    return (((uint16_t)internalData.scale)*9)>>8;
}
uint8_t SongData::GetBpm()
{
    return internalData.bpm;
}

uint8_t SongData::GetPlayingPattern()
{
    return internalData.playingPattern;
}
void    SongData::SetPlayingPattern(uint8_t playingPattern)
{
    internalData.playingPattern = playingPattern;
}

void SongData::LoadPatternChain(int *patternChain)
{
    for(int i=0;i<16;i++)
    {
        patternChain[i] = internalData.patternChain[i];
    }
}
void SongData::StorePatternChain(int *patternChain)
{
    for(int i=0;i<16;i++)
    {
        internalData.patternChain[i] = patternChain[i];
    }
}

uint8_t SongData::GetPatternChainLength()
{
    return internalData.patternChainLength;
}
void    SongData::SetPatternChainLength(uint8_t patternChainLength)
{
    internalData.patternChainLength = patternChainLength;
}


const int keyMap[16] = {
    12, 13, 14, 15,
    8, 9, 10, 11,
    4, 5, 6, 7,
    0, 1, 2, 3
};

const int scales[] = {
    0, 2, 4, 5, 7, 9, 11, //Maj
    0, 2, 3, 5, 7, 8, 10, //NMin
    0, 2, 3, 5, 7, 8, 11, //HMin
    0, 2, 3, 5, 7, 9, 11, //MMin
    0, 2, 3, 5, 7, 9, 10, //Dor
    0, 1, 3, 5, 7, 8, 10, //Phry
    0, 2, 4, 6, 7, 9, 11, //Lyd
    0, 2, 4, 5, 7, 9, 10, //Mixo
    0, 1, 3, 5, 6, 8, 10, //Locr
};

uint8_t SongData::GetNote(uint8_t key, int8_t octave)
{
    key = keyMap[key];
    return scales[GetScale()*7+key%7]+12*(key/7)+12*octave+GetRoot() + 60;
}

const char *syncOutStrings[6] = { 
    "none",
    "midi",
    "m+PO",
    "m+4P",
    "PO",
    "4PPQ"
};
const char *syncInStrings[4] = { 
    "none",
    "midi",
    "PO",
    "4PPQ",
};
const char *rootStrings[12] = { 
    "C",
    "C#",
    "D",
    "D#",
    "E",
    "F",
    "F#",
    "G",
    "G#",
    "A",
    "A#",
    "B"
};


const char *scaleStrings[9] = {
"Maj",
"NMin",
"HMin",
"MMin",
"Dor",
"Phry",
"Lyd",
"Mixo",
"Locr"
};

void SongData::DrawParamString(uint8_t param, uint8_t pattern, char *str, int8_t octave)
{
    ssd1306_t* disp = GetDisplay();
    const uint8_t width = 36;
    const uint8_t column4 = 128-width;
    bool lockA = false, lockB = false;
    char *strA = str;
    char *strB = str+16;
    char *pA = str+32;
    char *pB = str+48;

    switch(param)
    {
        case 1:
            sprintf(strA, "chng");
            sprintf(pA, "%i", internalData.changeLength[pattern]/4+1);
            sprintf(strB, "");
            sprintf(pB,"");
            break;
        case 19:
            sprintf(strA, "bpm");
            if(GetSyncInMode()!=SyncModeNone)
            {
                sprintf(pA, "sync");
            }
            else
            {
                sprintf(pA, "%i", internalData.bpm+1);
            }
            sprintf(strB, "Swng");
            sprintf(pB, "%i", internalData.swing);
            break;
        case 19+25:    // 44
            sprintf(strA, "SncI");
            sprintf(pA, syncInStrings[(internalData.syncIn*4)>>8]);
            sprintf(strB, "SncO");
            sprintf(pB, syncOutStrings[(internalData.syncOut*6)>>8]);
            break;
        case 19+25+25: // 69
            sprintf(strA, "vol");
            sprintf(pA, "%i", GetHPVol());
            sprintf(strB, "");
            sprintf(pB, "");
            break;
        case 24:
            sprintf(strA, "Octv");
            sprintf(pA, "%i", octave);
            sprintf(strB, "Root");
            sprintf(pB,rootStrings[GetRoot()]);
            break;
        case 24+25:
            sprintf(strA, "Scle");
            sprintf(pA, scaleStrings[GetScale()]);
            sprintf(strB, "");
            sprintf(pB,"");
            break;
        case 22+25:
            sprintf(strA, "DlFb");
            sprintf(pA, "%i", internalData.delayFeedback);
            sprintf(strB, "DlTm");
            sprintf(pB, "%i", internalData.delayTime);
            break;
        case 22+25+25:
            sprintf(strA, "VbFb");
            sprintf(pA, "%i", internalData.reverbFeedback);
            sprintf(strB, "VbDm");
            sprintf(pB, "%i", internalData.reverbDamping);
            break;
        case 22+25+25+25:
            sprintf(strA, "VbMd");
            sprintf(pA, "%i", internalData.reverbModulation);
            sprintf(strB, "VbTy");
            sprintf(pB, GetReverbLongTail()?"Lng":"Srt");
            break;
    }
    
    ssd1306_draw_string_gfxfont(disp, column4+3, 12, str+32, true, 1, 1, &m6x118pt7b);
    ssd1306_draw_string_gfxfont(disp, column4+3, 17+12, str+48, true, 1, 1, &m6x118pt7b);
    
    ssd1306_draw_string_gfxfont(disp, column4-33, 12, str, true, 1, 1, &m6x118pt7b);    
    ssd1306_draw_string_gfxfont(disp, column4-33, 17+12, str+16, true, 1, 1, &m6x118pt7b);
}

void SongData::Serialize(pb_ostream_t *s)
{
    pb_encode_ex(s, SongDataInternal_fields, &internalData, PB_ENCODE_DELIMITED);
}

void SongData::Deserialize(pb_istream_t *s)
{
    if(!pb_decode_ex(s, SongDataInternal_fields, &internalData, PB_ENCODE_DELIMITED))
    {
        const char * error = PB_GET_ERROR(s);
        printf("SongData deserialize error: %s\n", error);
    }
    // songs written before the reverb had its own page carry no reverb settings at
    // all, so they open on the defaults. that is not the tuning they were made
    // against - the old tank had no working damping and rang for ~18s at 2kHz
    if(!internalData.has_reverbFeedback)
    {
        internalData.has_reverbFeedback = true;
        internalData.reverbFeedback = VERB_DEFAULT_FEEDBACK;
    }
    if(!internalData.has_reverbDamping)
    {
        internalData.has_reverbDamping = true;
        internalData.reverbDamping = VERB_DEFAULT_DAMPING;
    }
    if(!internalData.has_reverbModulation)
    {
        internalData.has_reverbModulation = true;
        internalData.reverbModulation = VERB_DEFAULT_MODULATION;
    }
    // songs saved before this field existed - including ones still carrying the
    // old reverbLowCap on tag 18 - open on the long tail, which is what the reverb
    // did before the switch existed
    if(!internalData.has_reverbLongTail)
    {
        internalData.has_reverbLongTail = true;
        internalData.reverbLongTail = 0xff;
    }
}
